melka/dactyl-keyboard/parts/promicro/MICRO_stackable header pin.SLDPRT

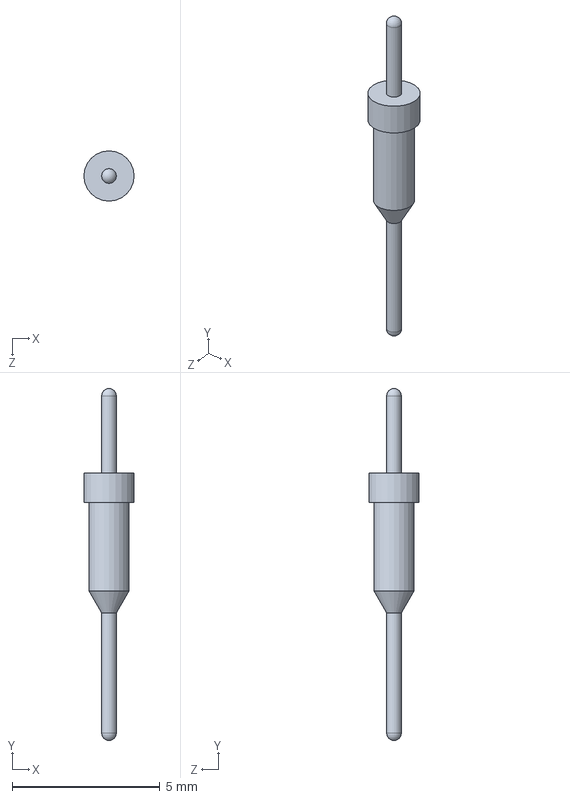
[picture p22: CAD file, 2021-06-02]
parts/promicro/MICRO_stackable header pin.SLDPRT
1.70 x 11.9 x 1.70 mm
