melka/dactyl-keyboard/step/right_clean.step

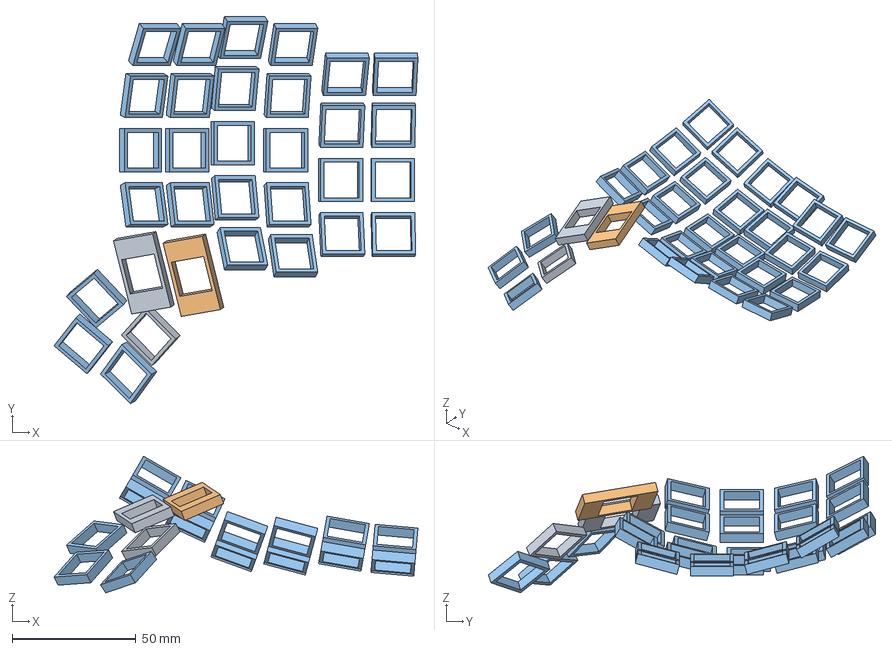
[picture p23: CAD file, 2021-06-01]
step/right_clean.step
146.8 x 156.1 x 55.1 mm
