melka/dactyl-keyboard/parts/DSA Keycap Project/DSA 1.75u.step

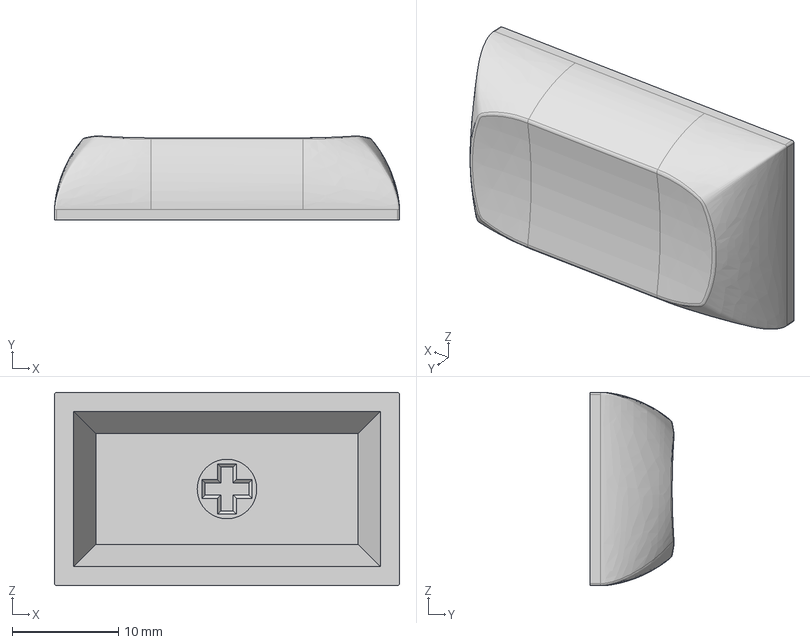
[picture p24: CAD file, 2021-06-02]
parts/DSA Keycap Project/DSA 1.75u.step
32.5 x 7.91 x 18.2 mm
