melka/dactyl-keyboard/parts/DSA Keycap Project/DSA 2.25u.step

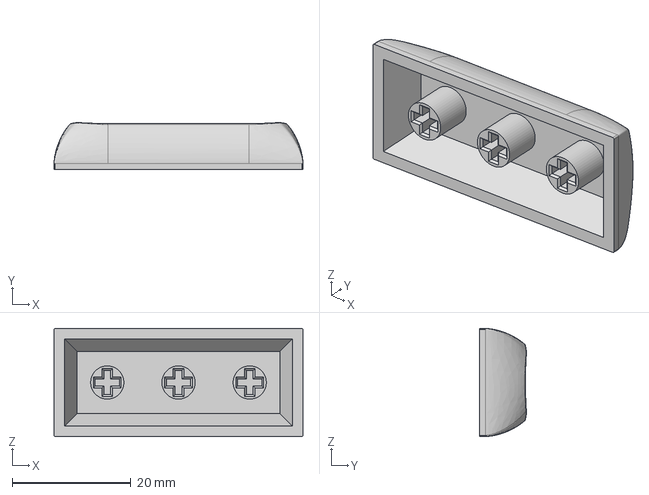
[picture p25: CAD file, 2021-06-02]
parts/DSA Keycap Project/DSA 2.25u.step
42.0 x 7.91 x 18.2 mm
