melka/dactyl-keyboard/parts/mx/针脚.SLDPRT

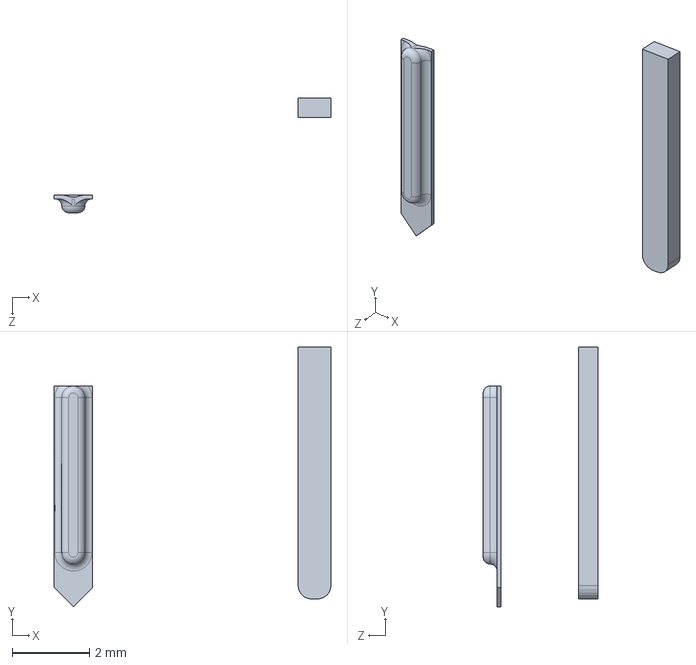
[picture p26: CAD file, 2021-06-02]
parts/mx/针脚.SLDPRT
7.15 x 6.70 x 2.96 mm
