melka/dactyl-keyboard/parts/promicro/micro_crystal 5x3.SLDPRT

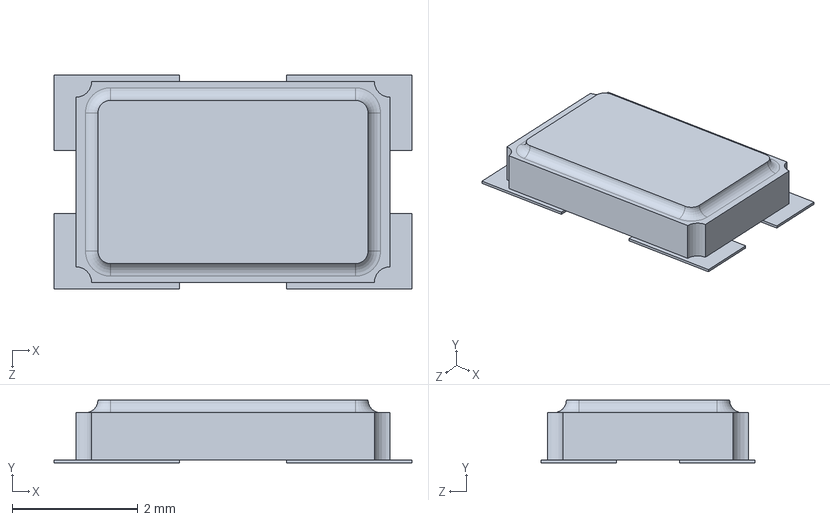
[picture p27: CAD file, 2021-06-02]
parts/promicro/micro_crystal 5x3.SLDPRT
5.70 x 1.00 x 3.40 mm
