melka/dactyl-keyboard/parts/DSA Keycap Project/DSA 1.5u.step

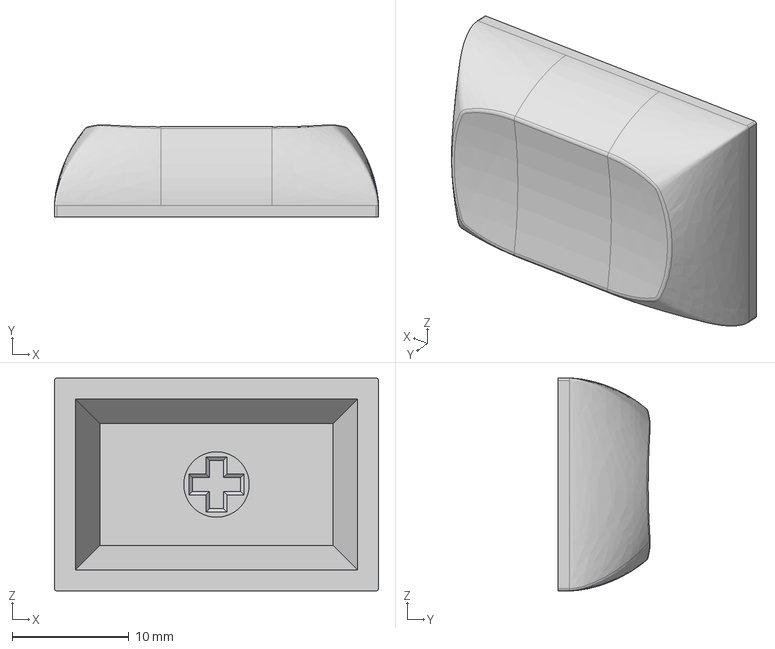
[picture p28: CAD file, 2021-06-02]
parts/DSA Keycap Project/DSA 1.5u.step
27.7 x 7.91 x 18.2 mm
