melka/dactyl-keyboard/parts/mx/MX 轴 按键.SLDPRT

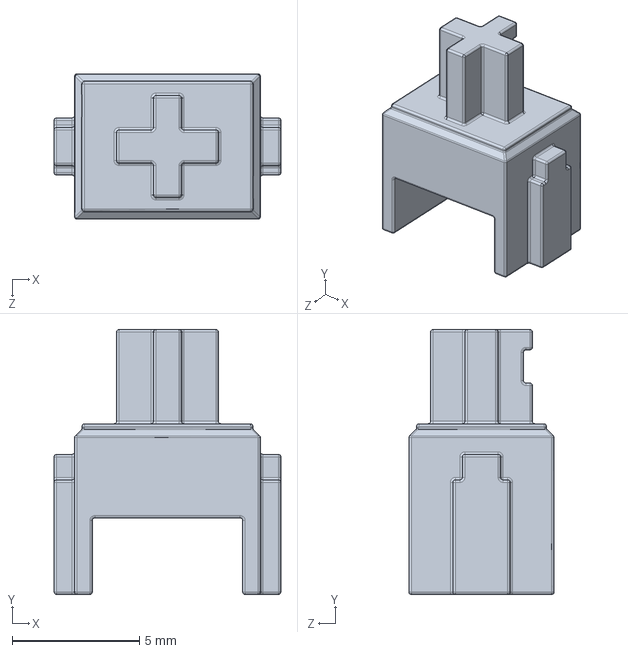
[picture p29: CAD file, 2021-06-02]
parts/mx/MX 轴 按键.SLDPRT
8.90 x 10.4 x 5.70 mm
