melka/dactyl-keyboard/parts/promicro/micro usb contact.SLDPRT

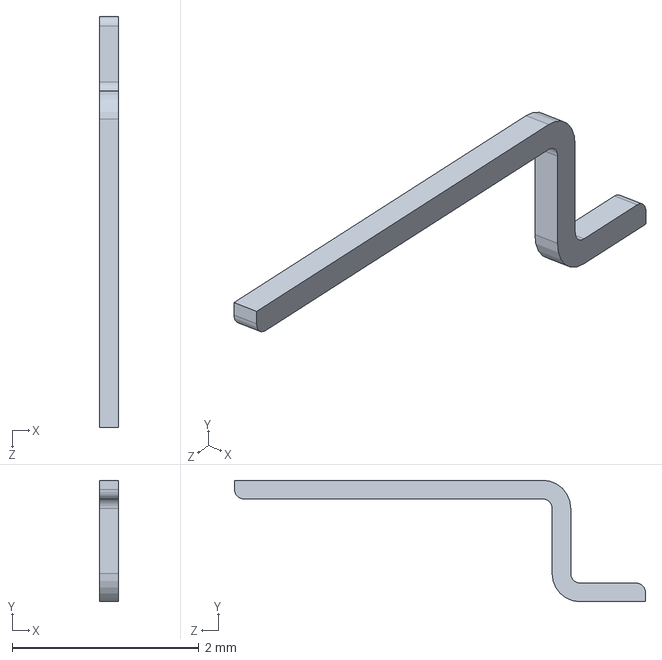
[picture p30: CAD file, 2021-06-02]
parts/promicro/micro usb contact.SLDPRT
0.2 x 1.30 x 4.40 mm
