melka/dactyl-keyboard/parts/DSA Keycap Project/DSA 1u.step

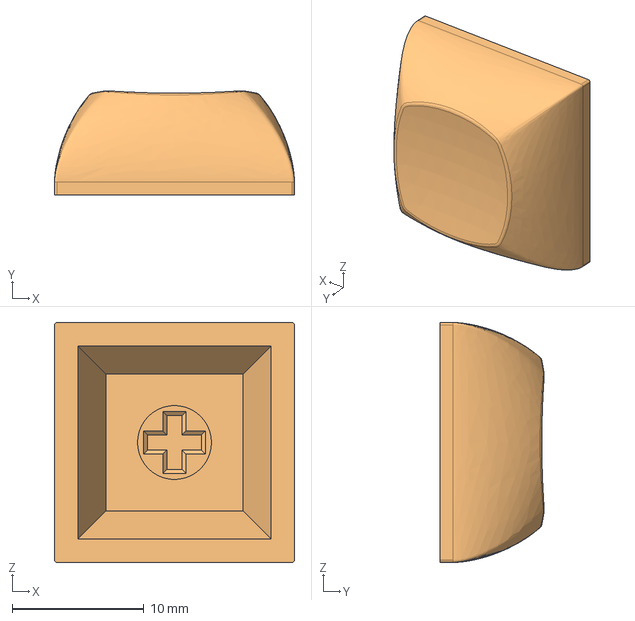
[picture p31: CAD file, 2021-06-02]
parts/DSA Keycap Project/DSA 1u.step
18.2 x 7.91 x 18.2 mm
