melka/dactyl-keyboard/parts/mx/MX轴 无帽LED.SLDPRT

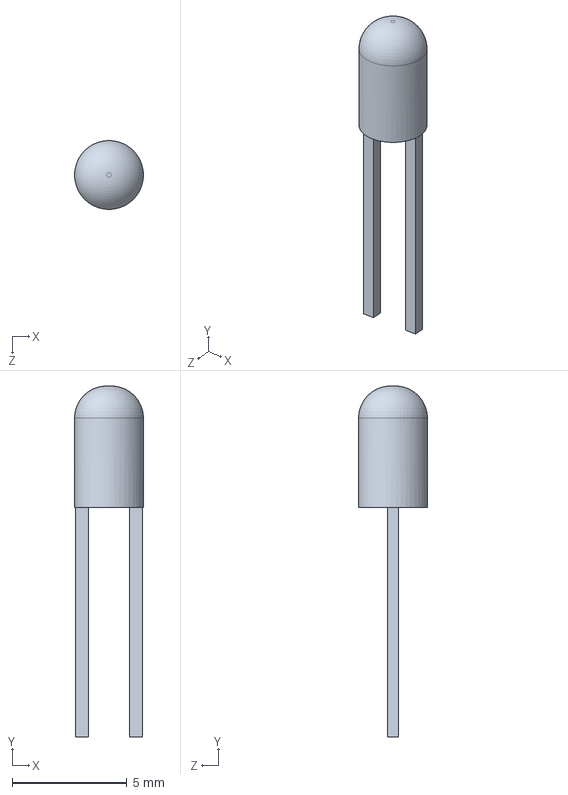
[picture p32: CAD file, 2021-06-02]
parts/mx/MX轴 无帽LED.SLDPRT
3.00 x 15.3 x 3.00 mm
