melka/dactyl-keyboard/parts/promicro/micro board.SLDPRT

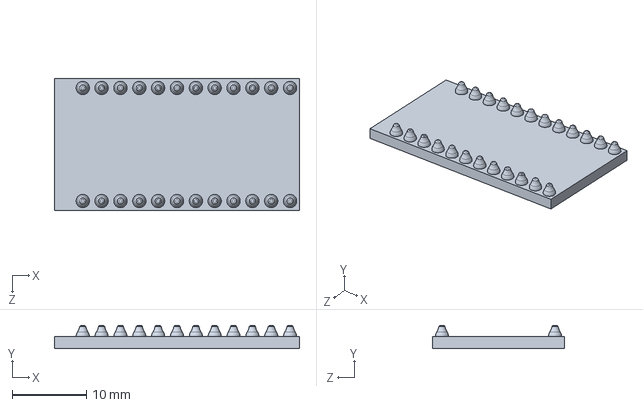
[picture p33: CAD file, 2021-06-02]
parts/promicro/micro board.SLDPRT
33.0 x 3.10 x 17.8 mm
