melka/dactyl-keyboard/parts/DSA Keycap Project/DSA 1.25u.stl

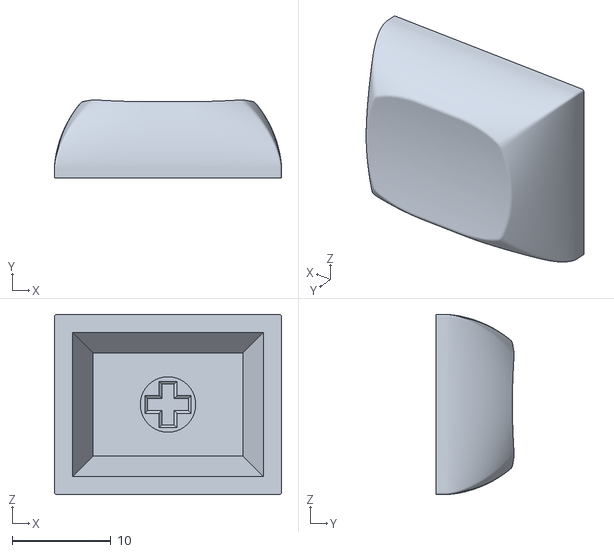
[picture p34: CAD file, 2021-06-02]
parts/DSA Keycap Project/DSA 1.25u.stl
23.0 x 7.91 x 18.2
