melka/dactyl-keyboard/parts/promicro/MICRO_603 cap on pad.SLDPRT

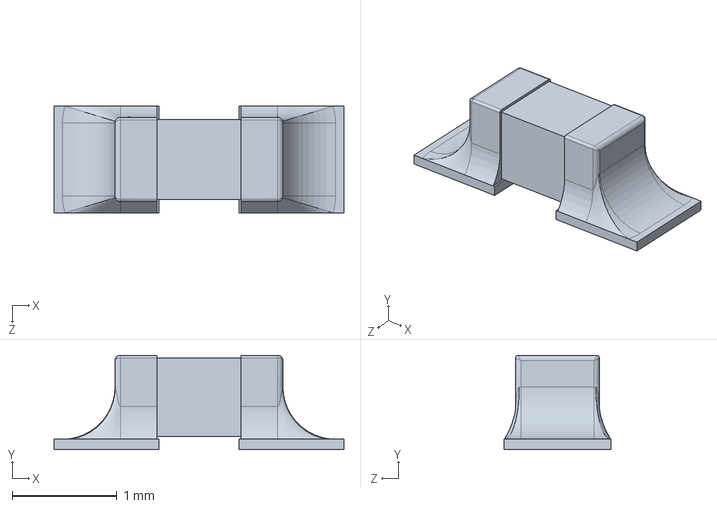
[picture p35: CAD file, 2021-06-02]
parts/promicro/MICRO_603 cap on pad.SLDPRT
2.76 x 0.9 x 1.02 mm
