melka/dactyl-keyboard/parts/promicro/MICRO_603 resistor 103.SLDPRT

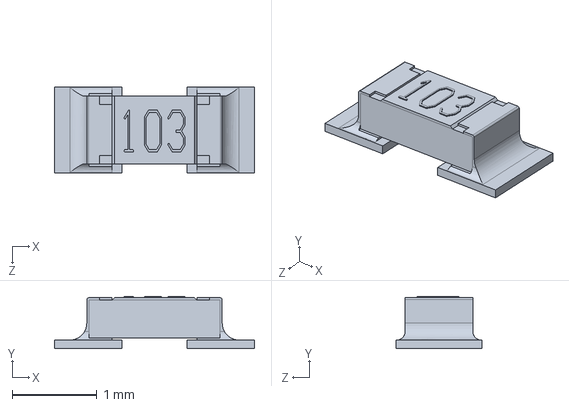
[picture p36: CAD file, 2021-06-02]
parts/promicro/MICRO_603 resistor 103.SLDPRT
2.36 x 0.615 x 1.02 mm
