melka/dactyl-keyboard/parts/promicro/MICRO_cap106C.SLDPRT

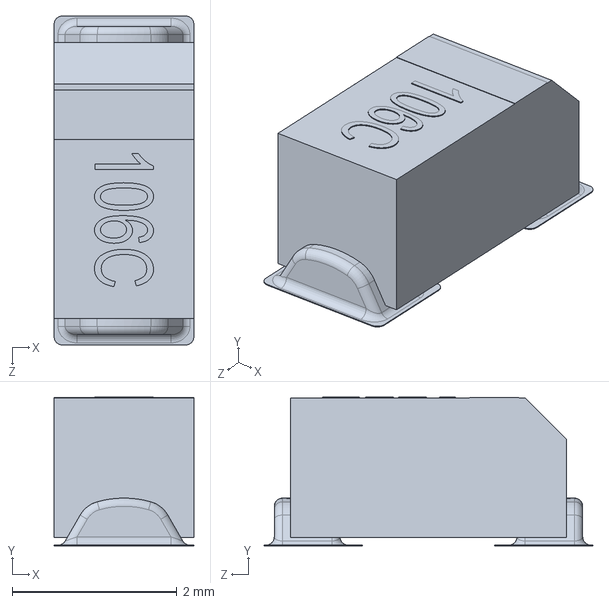
[picture p37: CAD file, 2021-06-02]
parts/promicro/MICRO_cap106C.SLDPRT
1.70 x 1.81 x 4.00 mm
