melka/dactyl-keyboard/parts/promicro/micro usb internal.SLDPRT

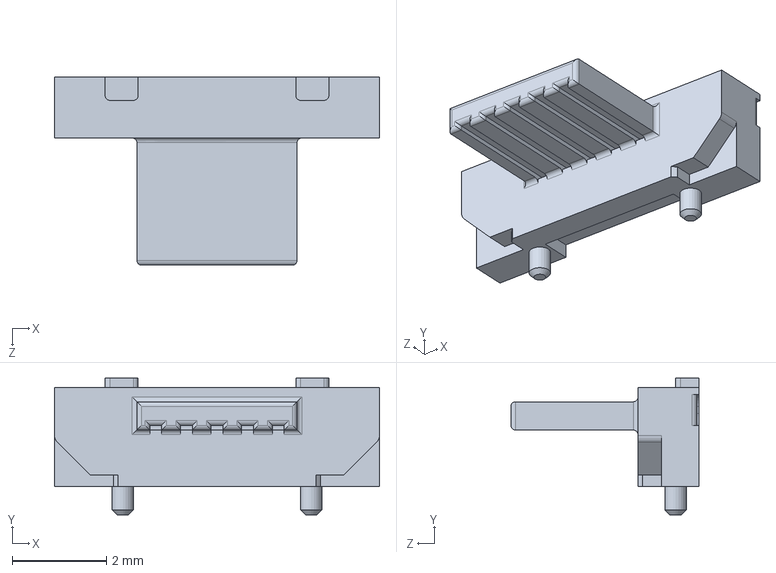
[picture p38: CAD file, 2021-06-02]
parts/promicro/micro usb internal.SLDPRT
6.90 x 2.90 x 4.00 mm
