melka/dactyl-keyboard/parts/promicro/MICRO_PTC-1206.SLDPRT

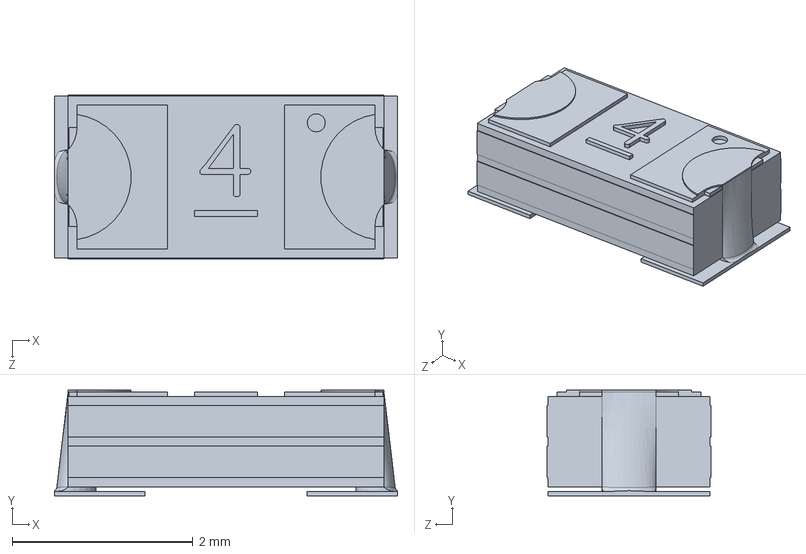
[picture p39: CAD file, 2021-06-02]
parts/promicro/MICRO_PTC-1206.SLDPRT
3.80 x 1.17 x 1.82 mm
