melka/dactyl-keyboard/parts/promicro/MICRO_led.SLDPRT

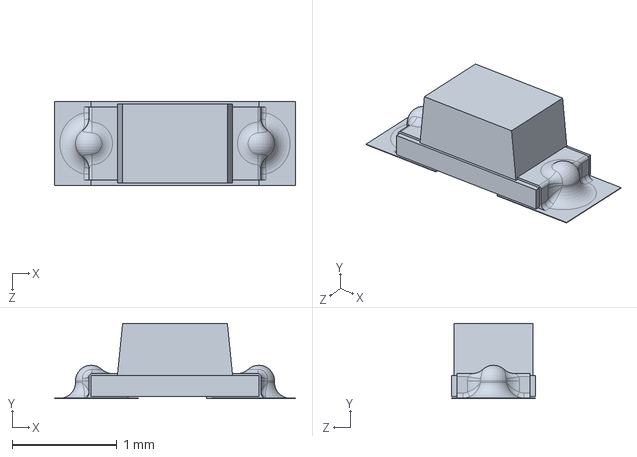
[picture p40: CAD file, 2021-06-02]
parts/promicro/MICRO_led.SLDPRT
2.30 x 0.72 x 0.8 mm
