melka/dactyl-keyboard/parts/promicro/micro usb shell.SLDPRT

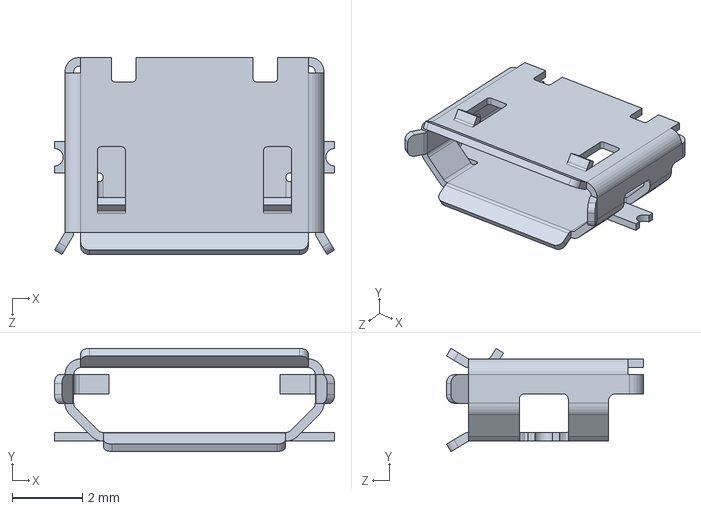
[picture p41: CAD file, 2021-06-02]
parts/promicro/micro usb shell.SLDPRT
8.00 x 2.95 x 5.63 mm
