melka/dactyl-keyboard/parts/promicro/micro_MIC5219.SLDPRT

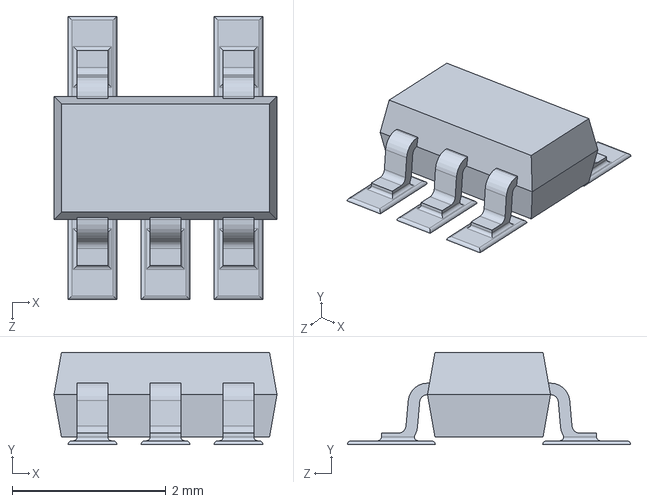
[picture p42: CAD file, 2021-06-02]
parts/promicro/micro_MIC5219.SLDPRT
2.90 x 1.20 x 3.68 mm
