melka/dactyl-keyboard/parts/promicro/SOD 323.SLDPRT

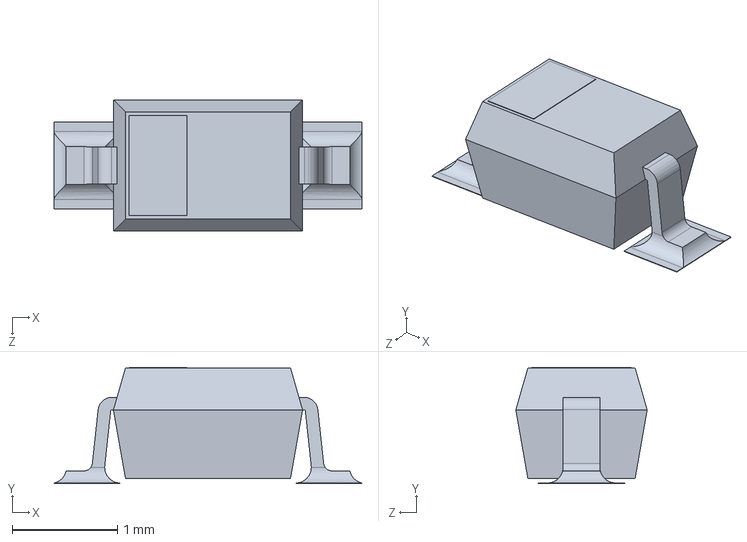
[picture p43: CAD file, 2021-06-02]
parts/promicro/SOD 323.SLDPRT
2.93 x 1.11 x 1.25 mm
